ttkpark/SmartBox/01.분석및설계/Image/20200304_221038.jpg

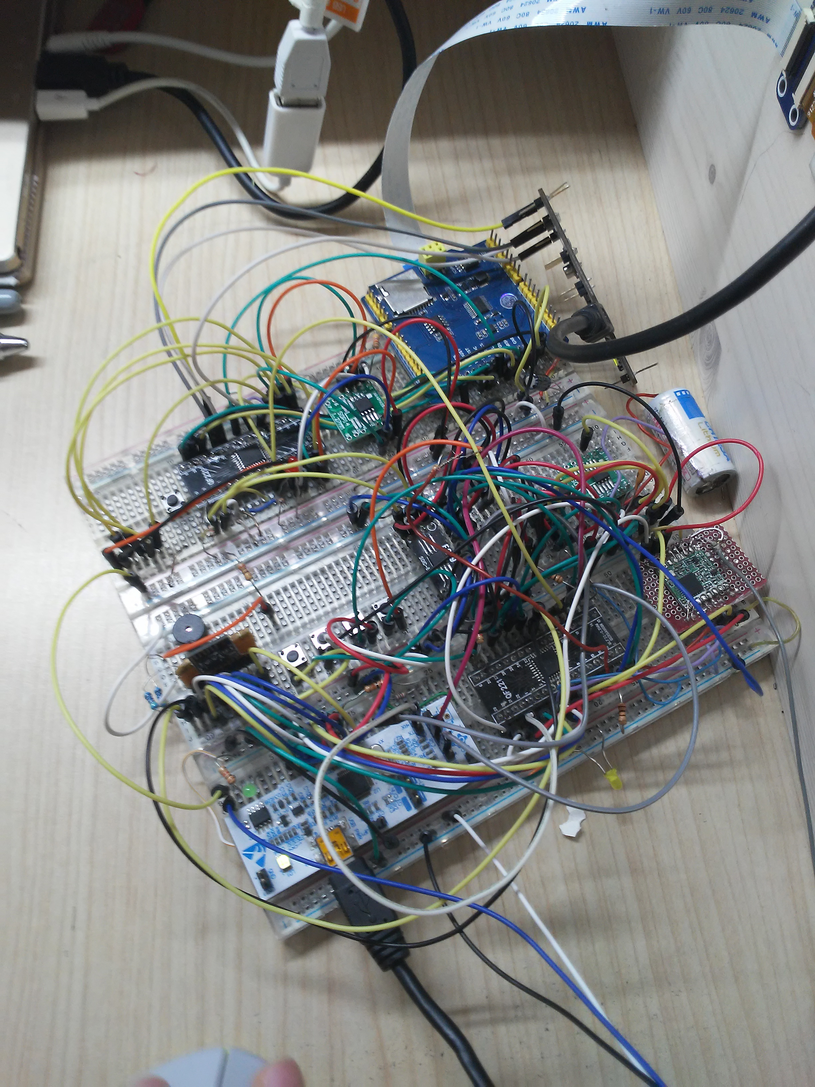
01.분석및설계/Image/20200304_221038.jpg
