ttkpark/SmartBox/회로/ORCAD/RFM95.jpg

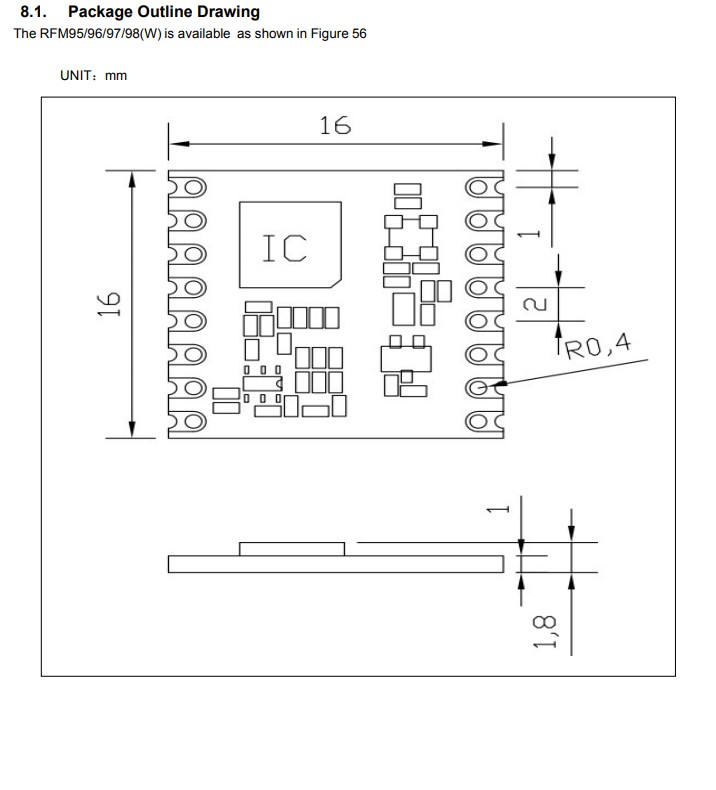
회로/ORCAD/RFM95.jpg
