ttkpark/SmartBox/회로/ORCAD/UFL.jpg

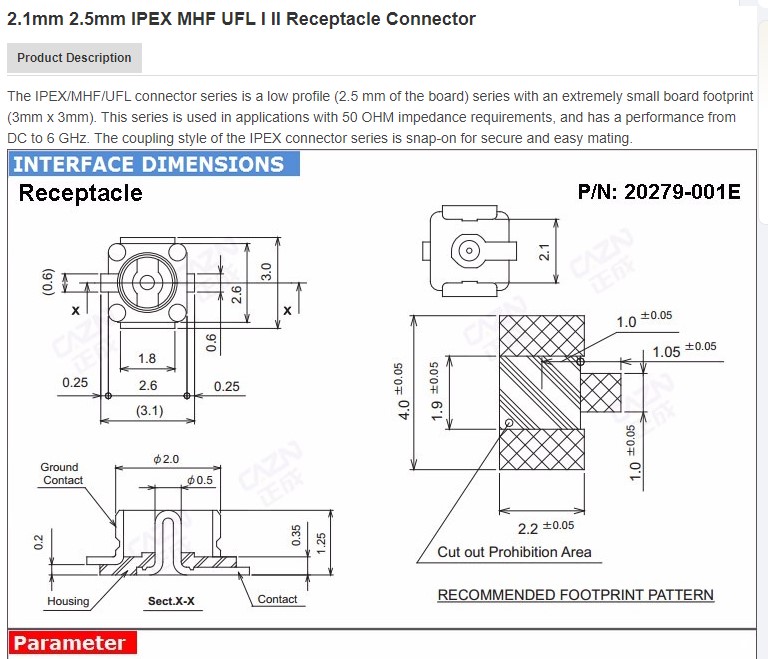
회로/ORCAD/UFL.jpg
