ttkpark/SmartBox/3D Model/Workzone/Body/Body_Top.stl

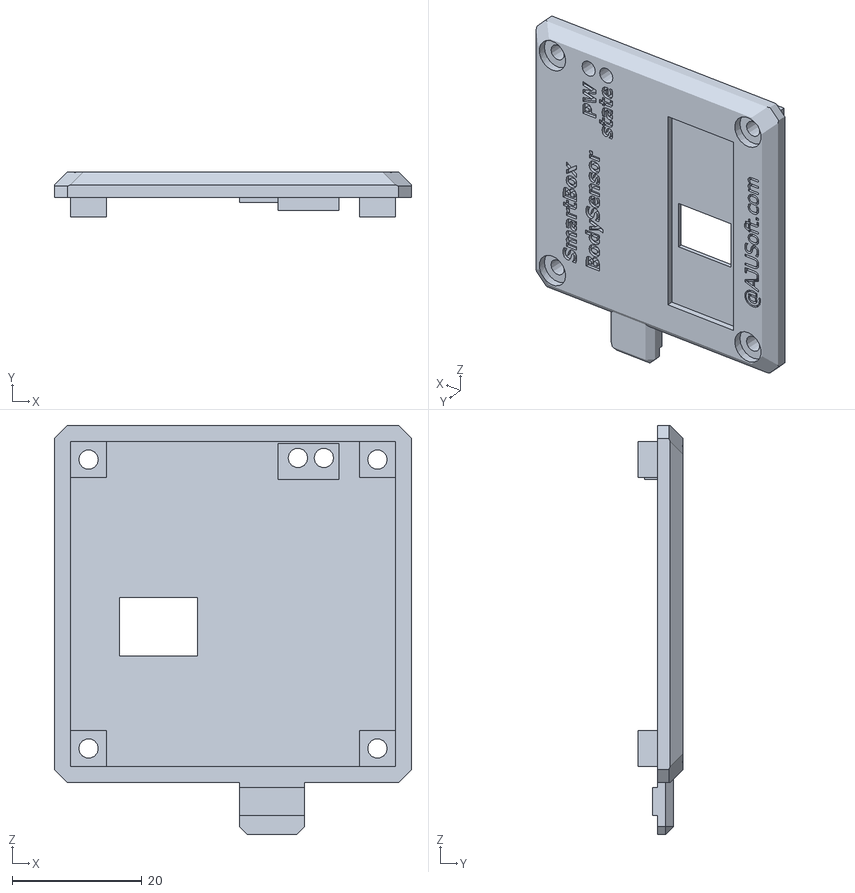
[picture p66: CAD file, 2023-04-14]
3D Model/Workzone/Body/Body_Top.stl
55.0 x 7.00 x 63.0
