ttkpark/SmartBox/3D Model/Charger/Charger_Top.stl

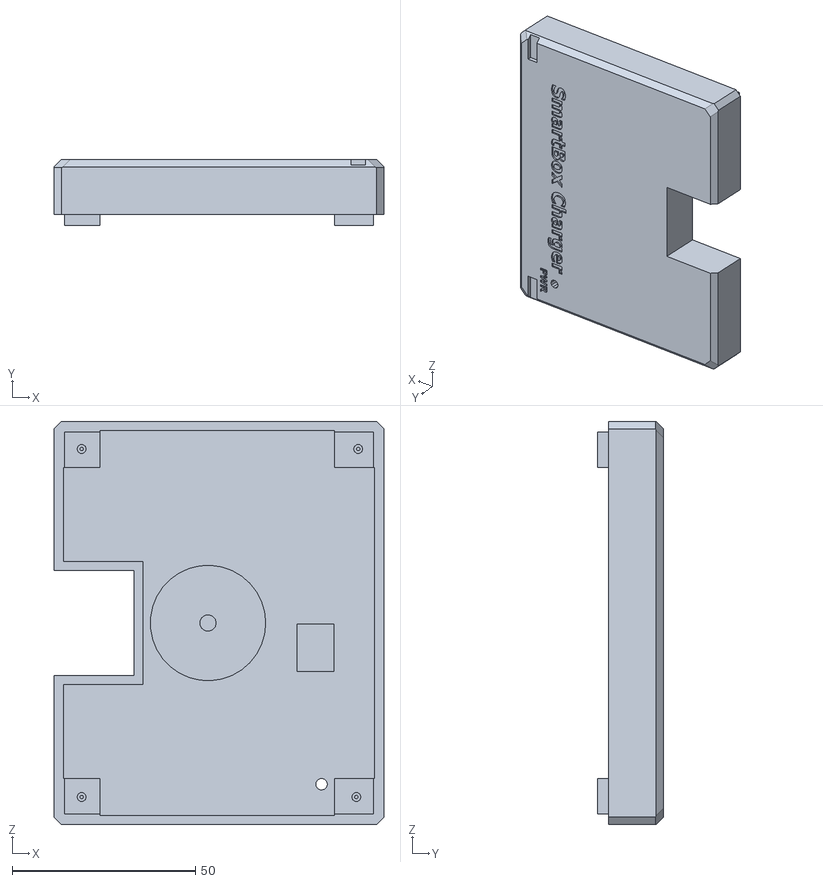
[picture p67: CAD file, 2023-04-14]
3D Model/Charger/Charger_Top.stl
90.0 x 18.0 x 110.0
