ttkpark/SmartBox/3D Model/SmartBox/Button.stl

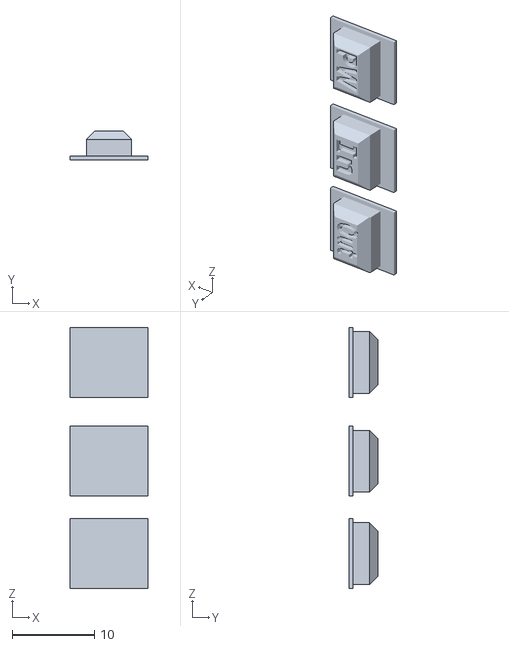
[picture p68: CAD file, 2023-04-14]
3D Model/SmartBox/Button.stl
9.50 x 3.50 x 31.8
