ttkpark/SmartBox/3D Model/SmartBox/SmartBox3_Bottom.stl

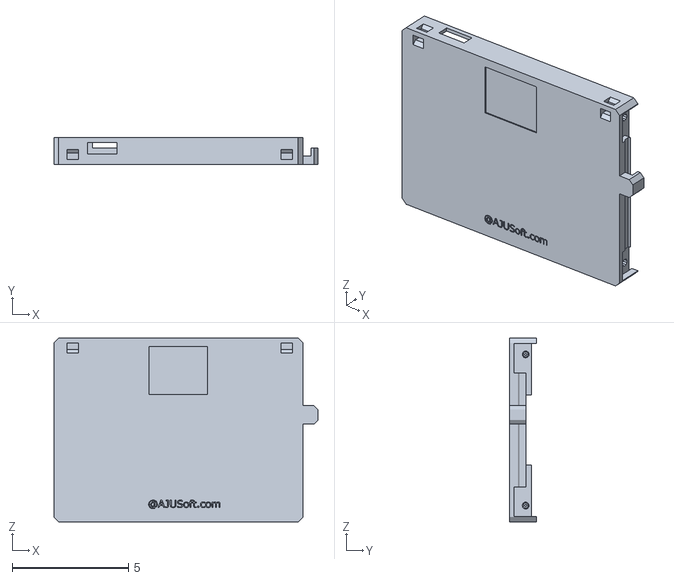
[picture p69: CAD file, 2023-04-14]
3D Model/SmartBox/SmartBox3_Bottom.stl
11.3 x 1.15 x 7.90
