ttkpark/SmartBox/WZMS_Sensors Code/WZMS_Outer_HT_Lora/Inc/main.h

#define LORA_DIO1_Pin GPIO_PIN_0
#define LORA_DIO1_GPIO_Port GPIOA
#define LORA_DIO1_EXTI_IRQn EXTI0_IRQn
#define NRF_CE_Pin GPIO_PIN_3
#define NRF_CE_GPIO_Port GPIOA
#define NRF_CSN_Pin GPIO_PIN_4
#define NRF_CSN_GPIO_Port GPIOA
#define LORA_NSS_Pin GPIO_PIN_0
#define LORA_NSS_GPIO_Port GPIOB
#define LORA_DIO0_Pin GPIO_PIN_1
#define LORA_DIO0_GPIO_Port GPIOB
#define LORA_DIO0_EXTI_IRQn EXTI1_IRQn
#define DebugLED_Pin GPIO_PIN_8
#define DebugLED_GPIO_Port GPIOA
#define SW_Reset_Pin GPIO_PIN_11
#define SW_Reset_GPIO_Port GPIOA
#define SW_Reset_EXTI_IRQn EXTI15_10_IRQn
#define LED_RED_Pin GPIO_PIN_4
#define LED_RED_GPIO_Port GPIOB
#define LED_GREEN_Pin GPIO_PIN_5
#define LED_GREEN_GPIO_Port GPIOB
